gevv/arduino-battery-analyzer/frimware/batmeter_nano/lcd_customchars.h

char customchar1[] = \
{
    0b01110,
    0b11111,
    0b11111,
    0b11111,
    0b11111,
    0b11111,
    0b11111,
    0000000
};

char customchar2[] = \
{
    0b01110,
    0b11011,
    0b10001,
    0b11111,
    0b11111,
    0b11111,
    0b11111,
    0000000
};

char customchar3[] = \
{
    0b01110,
    0b11011,
    0b10001,
    0b10001,
    0b11111,
    0b11111,
    0b11111,
    0000000
};

char customchar4[] = \
{
    0b01110,
    0b11011,
    0b10001,
    0b10001,
    0b10001,
    0b11111,
    0b11111,
    0000000
};

char customchar5[] = \
{
    0b01110,
    0b11011,
    0b10001,
    0b10001,
    0b10001,
    0b10001,
    0b11111,
    0000000
};

#define OMEGA_CHAR 5

char customchar6[] = \
{
    0b00000,
    0b01110,
    0b10001,
    0b10001,
    0b01010,
    0b11011,
    0b00000,
    0000000
};
